Aberdeen-Skunkworks/AccousticLevitator/FPGA/dac.v

`timescale 100 ps / 10 ps
//This is a Delta-Sigma Digital to Analog Converter
module dac#(parameter MSBI=7)(DACout, DACin, Clk, Reset);
output DACout; // This is the average output that feeds low pass filter
reg DACout; // for optimum performance, ensure that this ff is in IOB
input [MSBI+1:0] DACin; // DAC input (excess 2**MSBI)
input Clk;
input Reset;
reg [MSBI+2:0] DeltaAdder; // Output of Delta adder
reg [MSBI+2:0] SigmaAdder; // Output of Sigma adder
reg [MSBI+2:0] SigmaLatch; // Latches output of Sigma adder
reg [MSBI+2:0] DeltaB; // B input of Delta adder
always @(SigmaLatch) DeltaB = {SigmaLatch[MSBI+2], SigmaLatch[MSBI+2]} << (MSBI+1);
always @(DACin or DeltaB) DeltaAdder = DACin + DeltaB;
always @(DeltaAdder or SigmaLatch) SigmaAdder = DeltaAdder + SigmaLatch;
always @(posedge Clk or negedge Reset)
begin
	if(~Reset) begin
		SigmaLatch <= 1'b1 << (MSBI+1);
		DACout <= 1'b0;
	end else begin
		SigmaLatch <= SigmaAdder;
		DACout <= SigmaLatch[MSBI+2];
	end
end
endmodule
