Aberdeen-Skunkworks/AccousticLevitator/FPGA/divider.v

// fpga4student.com: FPGA projects, VHDL projects, Verilog projects
// Verilog project: Verilog code for clock divider on FPGA
// Top level Verilog code for clock divider on FPGA
module Clock_divider#(parameter BITS=8)(clock_in, clock_out, divisor, reset);
input clock_in; // input clock on FPGA
output clock_out; // output clock after dividing the input clock by divisor
input reset;
reg[BITS-1:0] counter;
input [BITS-1:0] divisor;

reg clock_out_driver;
always @(posedge clock_in or negedge reset)
begin
	if (~reset) begin
		counter <= {BITS{1'b0}};
		clock_out_driver <= 0;
	end else begin
		if(counter==divisor) begin
			counter <= {BITS{1'b0}};
			clock_out_driver <= ~clock_out_driver;
		end else begin
			counter <= counter + 1'b1;
		end
	end
end
assign clock_out = clock_out_driver;
endmodule
