Aberdeen-Skunkworks/AccousticLevitator/particle_simulation.py

import matplotlib as mpl; import numpy as np; import matplotlib.pyplot as plt; from mpl_toolkits.mplot3d import Axes3D;
import math; import algorithms; import transducer_placment; import phase_algorithms; import constants; import time
 
inital_pos = [0.001,0.001,0.021]            # m
inital_vel = [0,0,0]                        # m/s
gravity    = [0, 0, -9.81]                  # m/s^2
diamiter   = constants.particle_diamiter    # m    
density    = constants.rhos                 # kg/m^3
dt         = 0.0001                         # Time step s
end_time   = 0.5                            # End time s

time_steps = end_time/dt
print("Time steps = ", time_steps)
print("Rough Sim Legnth = ", round(time_steps*0.033, 2) , " seconds")

vol_sph =   constants.v                     # m^3
mass    = vol_sph * density                 # kg 


focus_point = [ 0 , 0, 0.02]
"""
##opposite arrays
focus_point = [ 0 , 0, 0.05]         # in the middle of the arrays
inital_pos = [0.001,0.001,0.051]
rt = transducer_placment.big_daddy()
ntrans = len (rt)   # Total number of transducers in grid
nt_1 = transducer_placment.direction_vectors(ntrans,[1,0,0]) # nt is the direction vector of each transducer
nt_2 = transducer_placment.direction_vectors(ntrans,[-1,0,0])

sideways_1 = np.copy(rt)
sideways_2 = np.copy(rt)

sideways_1[:,0] = np.add(rt[:,2], -0.0516)
sideways_1[:,2] = np.add(rt[:,0], 0.05)

sideways_2[:,0] = np.add(rt[:,2], 0.0516)
sideways_2[:,2] = np.add(rt[:,0], 0.05)

rt_both_arrays = np.append(sideways_1, sideways_2, axis=0)
nt_both_arrays = np.append(nt_1, nt_2, axis=0)
#transducer_placment.plot_as_vectors(rt_both_arrays,nt_both_arrays)  # Use to plot the array layout in 3D
rt = rt_both_arrays
nt = nt_both_arrays
"""

rt = transducer_placment.big_daddy()
ntrans = len (rt)
nt = transducer_placment.direction_vectors(ntrans,[0,0,1])
phi_focus = phase_algorithms.phase_find(rt, focus_point[0], focus_point[1], focus_point[2]) # phi is the initial phase of each transducer to focus on a point
phi = phase_algorithms.add_twin_signature(rt,phi_focus, 90)

x_distances = np.linspace(-constants.gsize + focus_point[0],   constants.gsize + focus_point[0], constants.npoints)
y_distances = np.linspace(-constants.gsize + focus_point[1],   constants.gsize + focus_point[1], constants.npoints)
z_distances = np.linspace(-constants.gsize + focus_point[2],   constants.gsize + focus_point[2], constants.npoints)

def find_nearest(array,value):
    idx = (np.abs(array-value)).argmin()
    return idx

number_of_time_steps = int( end_time / dt )

mass = np.copy(mass)
pos = np.copy(inital_pos)
vel = np.copy(inital_vel)
force_g = np.multiply( np.copy(gravity), mass)
total_energy = np.zeros(number_of_time_steps)

force_over_time = np.zeros((number_of_time_steps,3))
pos_over_time = np.zeros((number_of_time_steps,3))
x = np.zeros(number_of_time_steps); y = np.zeros(number_of_time_steps); z = np.zeros(number_of_time_steps)

"""
###### Forward Euler Algorithm
for time_step in range(0, number_of_time_steps):
    pos_over_time[time_step][0] = pos[0]; pos_over_time[time_step][1] = pos[1]; pos_over_time[time_step][2] = pos[2] 
    pos = np.add(pos,(np.multiply(dt, vel)))
    force = np.add( force_g, np.multiply(-1, algorithms.differentiate_acoustic_potential(dt,pos,rt,phi,nt)))
    vel = np.add(vel, (np.multiply(dt, np.divide(force, mass) ) ) )  
    time = np.add(time, dt)
    total_energy[time_step] = algorithms.acoustic_potential(pos, rt, phi, nt) + (0.5 * mass * np.linalg.norm(vel)**2) + (mass * 9.81 * pos[1])
    #if pos[1]<0:
    #    break
"""

force = np.add( force_g, np.multiply(-1, algorithms.differentiate_acoustic_potential(dt,pos,rt,phi,nt)))
acceleration = np.divide(force,mass)

print("Particle sim started")
t1 = time.time()
##### Verlet Algorithm Velocity       ### 1000 itterations took 32.7s 
for time_step in range(0, number_of_time_steps):
    pos_over_time[time_step][0] = pos[0]; pos_over_time[time_step][1] = pos[1]; pos_over_time[time_step][2] = pos[2] 
    
    pos = np.add( pos, np.multiply(dt, vel), (acceleration*( (dt**2) / 2 ) ) )
  
    force = np.add( force_g, np.multiply(-1, algorithms.differentiate_acoustic_potential(0.00000001,pos,rt,phi,nt)))

    acceleration_next = np.divide(force,mass)
    
    vel = np.add(vel, np.multiply( ( dt / 2 ) , np.add( acceleration, acceleration_next ) )   )
    
    acceleration = acceleration_next
    
    #total_energy[time_step] = algorithms.acoustic_potential(pos, rt, phi, nt) + (0.5 * mass * np.linalg.norm(vel)**2) + (mass * 9.81 * pos[2])
    if pos[2]<0:
        break
t2 = time.time()
print("Time Taken = ", round(t2-t1,2)," s")

fig = plt.figure()
ax = fig.gca(projection='3d')
ax.set_xlabel('xlabel')
ax.set_ylabel('ylabel')
ax.set_zlabel('zlabel')

###### turn to mm 
pos_over_time = np.multiply(1000, pos_over_time)

for time_step in range(0, number_of_time_steps):
    x[time_step] = pos_over_time[time_step][0]
    y[time_step] = pos_over_time[time_step][1]
    z[time_step] = pos_over_time[time_step][2]

yy, xx = np.meshgrid(np.linspace(-0.05, 0.05, num=21), np.linspace(-0.05, 0.05, num=21))
zz = xx*0

ax.plot(x, y, z, label='Trajectory')
ax.legend()


#fig = plt.figure()
#Energy Plot
#plt.plot(np.linspace(0,end_time,number_of_time_steps), total_energy, 'ro')
#plt.show()
